OLIMEX/NB-IoT/HARDWARE/NB-IoT-DevKit_Rev_D/3d/HN1x3-PinHeader_1x03_P2.54mm_Vertical.step

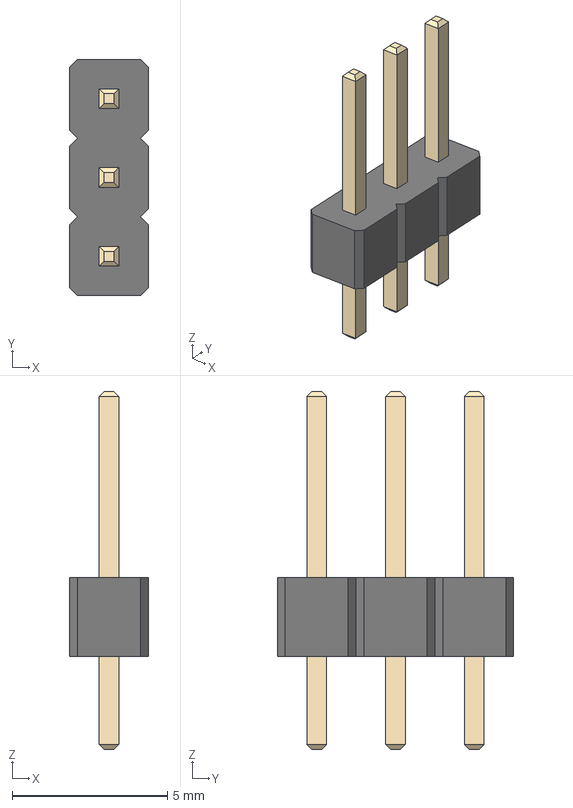
[picture p21: CAD file, 2019-10-17]
HARDWARE/NB-IoT-DevKit_Rev_D/3d/HN1x3-PinHeader_1x03_P2.54mm_Vertical.step
2.54 x 7.62 x 11.5 mm
