OLIMEX/NB-IoT/HARDWARE/NB-IoT-DevKit_Rev_D/3d/Molex_PicoBlade_530470210.step

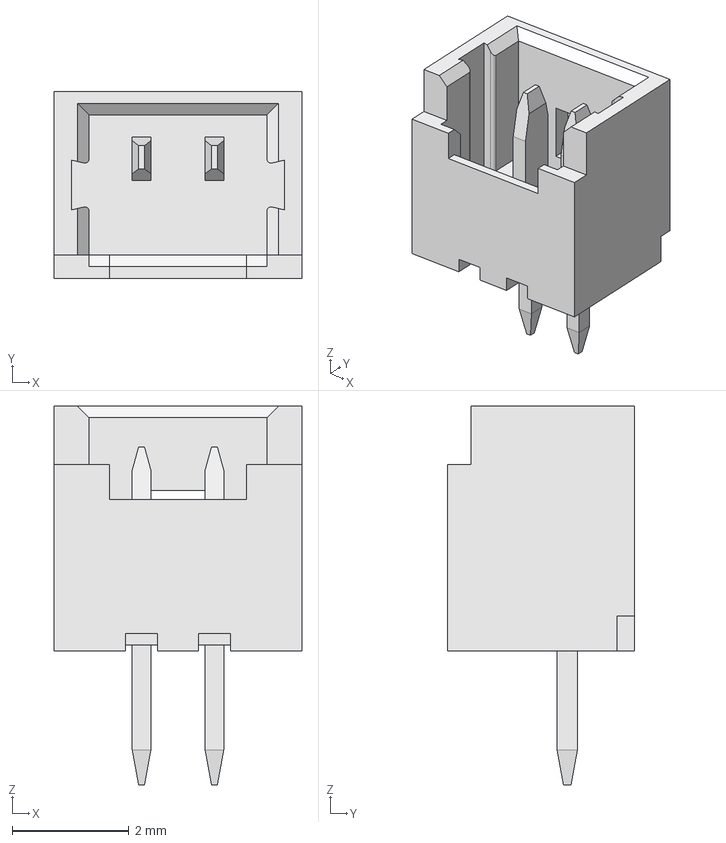
[picture p22: CAD file, 2019-10-17]
HARDWARE/NB-IoT-DevKit_Rev_D/3d/Molex_PicoBlade_530470210.step
4.25 x 3.20 x 6.50 mm
