OLIMEX/NB-IoT/HARDWARE/NB-IoT-DevKit_Rev_B/3d/NANO-SIM_Wurth_Electronics_693043020611.step

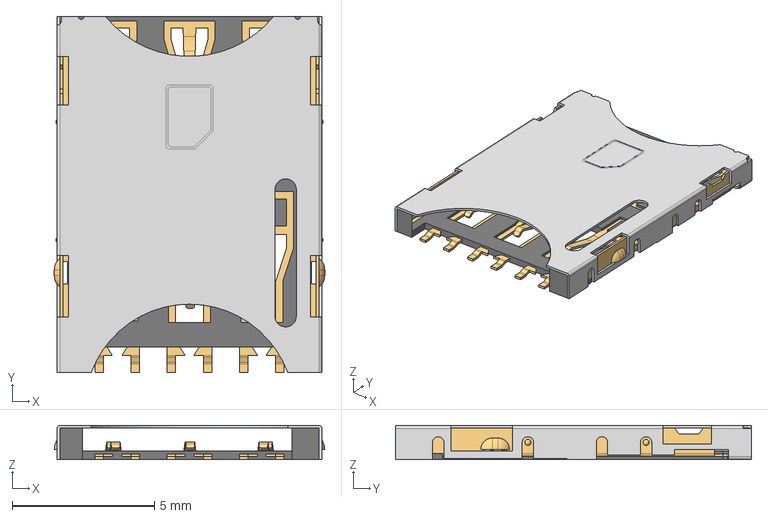
[picture p23: CAD file, 2019-10-17, an earlier design]
HARDWARE/NB-IoT-DevKit_Rev_B/3d/NANO-SIM_Wurth_Electronics_693043020611.step
9.50 x 12.5 x 1.21 mm
693043020611_SHIELDING
